raszpl/CL-GD542X_ISA/images/final.png

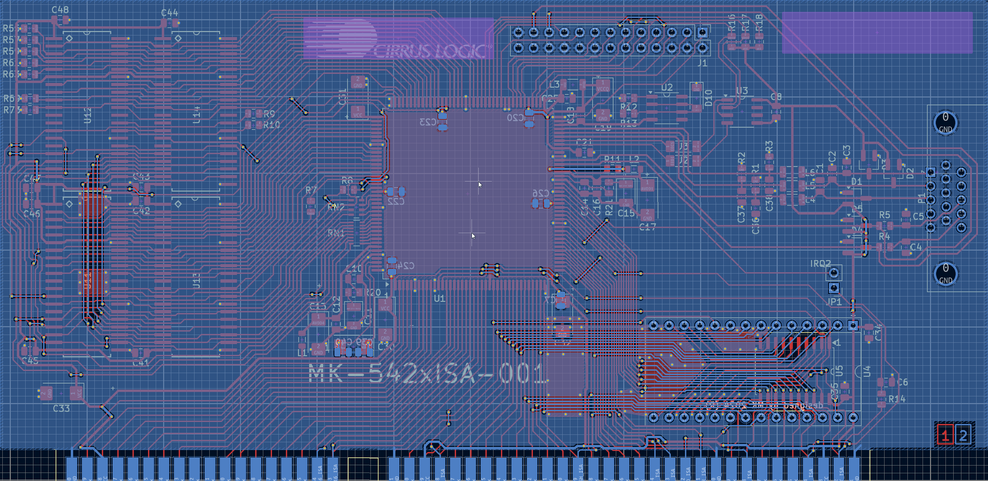
images/final.png
